AHA-Taiwan/2020_Taitung_Chulu-Between-Mountain-Clouds/002. Handbook/Constr-Process Handbook (pdf+ppt)/CBMC_Handbook.pdf

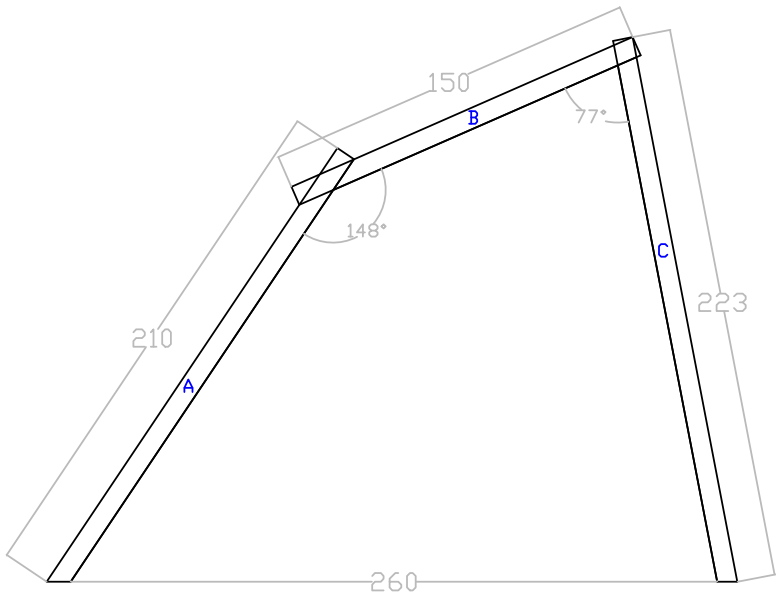
[picture p60: figure]
