AHA-Taiwan/2020_Taitung_Chulu-Between-Mountain-Clouds/002. Handbook/Constr-Process Handbook (pdf+ppt)/CBMC_Handbook.pdf

2020

# 初鹿義築．工作手冊

目錄

一．活動簡述．．．．．．．．．．．．１

二．自備物品與重要叮嚀．．．．．．．２

三．每日作息與行事曆．．．．．．．．４

四．交通與地圖．．．．．．．．．．．６

五．附件．．．．．．．．．．．．．．７

值日生班表

各組分工負責人

通訊錄

生活裝置設計圖面

木材尺寸

## 一．活動簡述

時間：2020年8月19日 —2020年8月28日

地點：台東縣卑南鄉初鹿國中（台東縣卑南鄉明峰村忠孝路2號） 住宿：初鹿國中圖書室

夏天是明亮的，太陽是辣的，
青春的心是熱血的。
離開了繁華，重返樸實；
捨棄了依賴，回歸自立。
參與團體 | 外界交流

俐場域建築設計

納樊司工作室

公東高工

家具木工科／室內設計科／建築科
義築工具圖書館

老麥農場露營區

台東縣政府文化處

社團法人台東縣巴蘭文化發展協會

社團法人台灣義築協會

聯新文教基金會

台東初鹿教會

行政院農委會林務局

正昌製材（台灣杉）

東皇昌五金行

材料贊助

１

## 二．自備物品與重要叮嚀

換洗衣物 | 輕便工作服／衣架／曬衣夾／塑膠袋／洗衣用具／肥皂
盥洗用品 | 潔牙用品／毛巾／沐浴用品／吹風機
個人衛生品 | 衛生紙／濕紙巾／生理用品
個人藥物 | 健保卡／防蚊液／防曬乳／藥膏／個人用藥
必備物品 | 手電筒／睡袋／麥克筆／抹布
餐具 | 環保餐具／水壺
其他 | 帽子／外套／雨具／筆記／糧食／相機／袖套 足夠的零用金＆快樂心
1. 校園蛇類出沒，夜間活動務必攜帶手電筒，並尊重當地生態環境 。
2. 為避免影響施工進度，請按作息表活動，請勿飲酒 。
3. 避免使用香味濃郁的盥洗用品，易引來蚊蟲 。
4. 請留意貴重物品 。
5. 請注意當地禁忌，活動請結伴同行 。
6. 當地提款與融資服務不便，請攜帶足夠的現金 。
7. 施工區域內請勿穿脫鞋或涼鞋，並時時補充水分。
8. 由於浴室數量有限，洗澡時間限制十分鐘。

重要叮嚀

２

施工注意事項

最重要的三件事！！

1. 晚間收工前30分鐘，清點材料、工具
2. 收工前15分鐘，整理工作環境
3. 工地危險，務必攜帶安全帽，勿著涼拖鞋

-工具配件務必妥善放回它的位置，切勿亂放

-建材勿隨意放置，會影響材料品質與建築壽命

-廢料勿扔棄，做好資源管理，這是對建築過程的尊重

-離隊務必告知組員、組長，個人行為將影響全體

-注意言行、態度，對自己負責，也尊重合作夥伴

-我們是一個大團體，務必保持與其他單位的良好互動

-我們是一個共同體，請關心身邊的伙伴，發揮自己的價值

做一個謙卑的實踐者，感恩這份學習的機會

３

## 三．每日作息與行事曆

時間 | 活動 | 備註
0600 | Good Morning | 宿舍長叫醒大家
0600–0630 | 盥洗準備
0630–0700 | 活力早餐 | 生活組提前準備
0700–1130 | 木構GO GO！ | 施工組開工
1130–1300 | 午餐充電 | 生活組準備
1300–1700 | 木構GO GO GO！ | 施工組開工
1700–1800 | 洗澎澎 | 超時斷水電！
1800–1930 | 晚餐時光 | 生活組準備
1930–2100 | 工作會議 | 進度／工地狀況檢討
2100–2200 | 小組／個人時間 | 工作日誌／影音整理
2200 | 睡飽睡好

生活值日生工作

1. 工作環境整理
2. 餐後、廚餘整理
3. 清洗、收拾餐具
4. 搬運、發放食物

住宿值日生工作

1. 寢室環境清潔
2. 廁所清潔及垃圾清理
3. 浴廁清潔

４

（時間可能依每日天候狀況有所調整）

08/19 （三）

08/20 （四）

08/21 （五）

08/22 （六）

行事曆

５

認識大家／基礎前置加工

08/23 （日）

08/24 （一）

08/26 （三）

08/25 （二）

08/28 （五）

08/27 （四）

基礎前置加工／放樣／灌漿

木料分類標號／尺寸標記

木構單元與基礎固定

木料加工：斬斷／引孔／導角

木構系統單元化組裝

木構系統單元化組裝

木料加工：斬斷／引孔／導角

表面處理／護木漆／環境清潔

表面處理／護木漆／環境清潔／撤收

## 四．交通與地圖

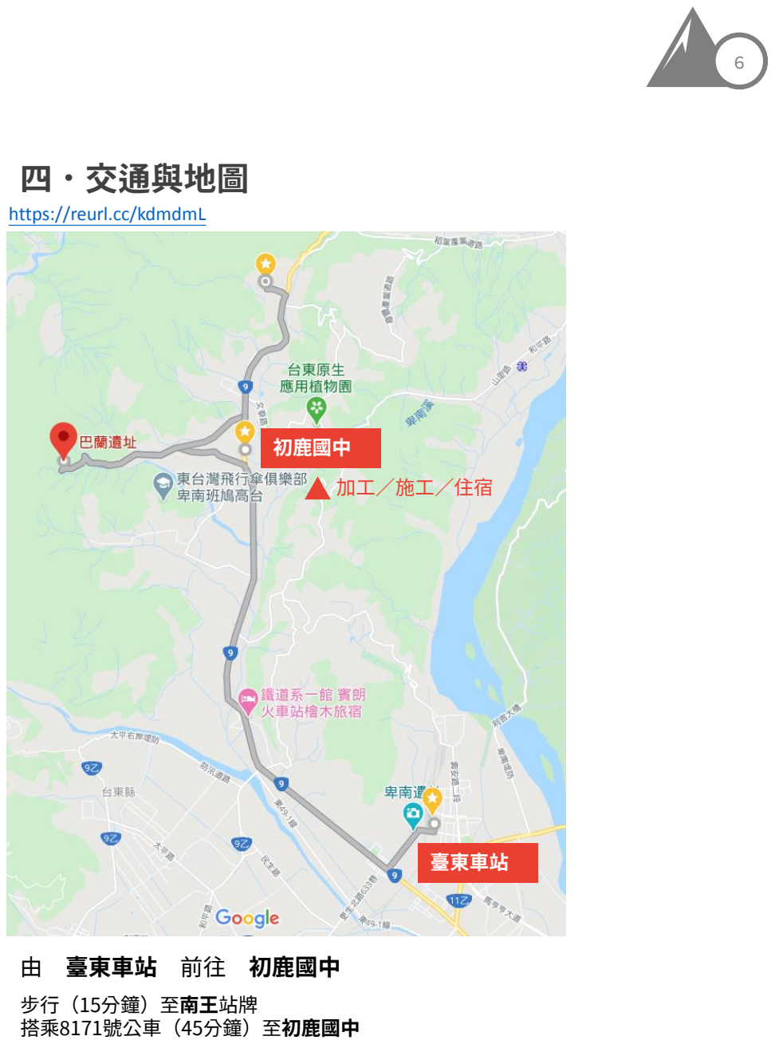
[picture p39: page 8]

由 臺東車站 前往 初鹿國中

初鹿國中

臺東車站

加工／施工／住宿

步行（15分鐘）至南王站牌
搭乘8171號公車（45分鐘）至初鹿國中

６

https://reurl.cc/kdmdmL

日期 | 生活值日生 | 住宿值日生
8/19 | 瑋聖 仁楷 | 正威 昊翰
8/20 | 偵慧 文慧 | 玥綾 柏翔
8/21 | 仁楷 正威 | 昊翰 震洋
8/22 | 文慧 玥綾 | 柏翔 甫亘
8/23 | 正威 昊翰 | 震洋 瑋聖
8/24 | 玥綾 柏翔 | 甫亘 偵慧
8/25 | 昊翰 震洋 | 瑋聖 仁楷
8/26 | 柏翔 甫亘 | 偵慧 文慧
8/27 | 震洋 瑋聖 | 仁楷 正威
8/28 | 甫亘 偵慧 | 文慧 玥綾

值日生班表

８

N1 | N2

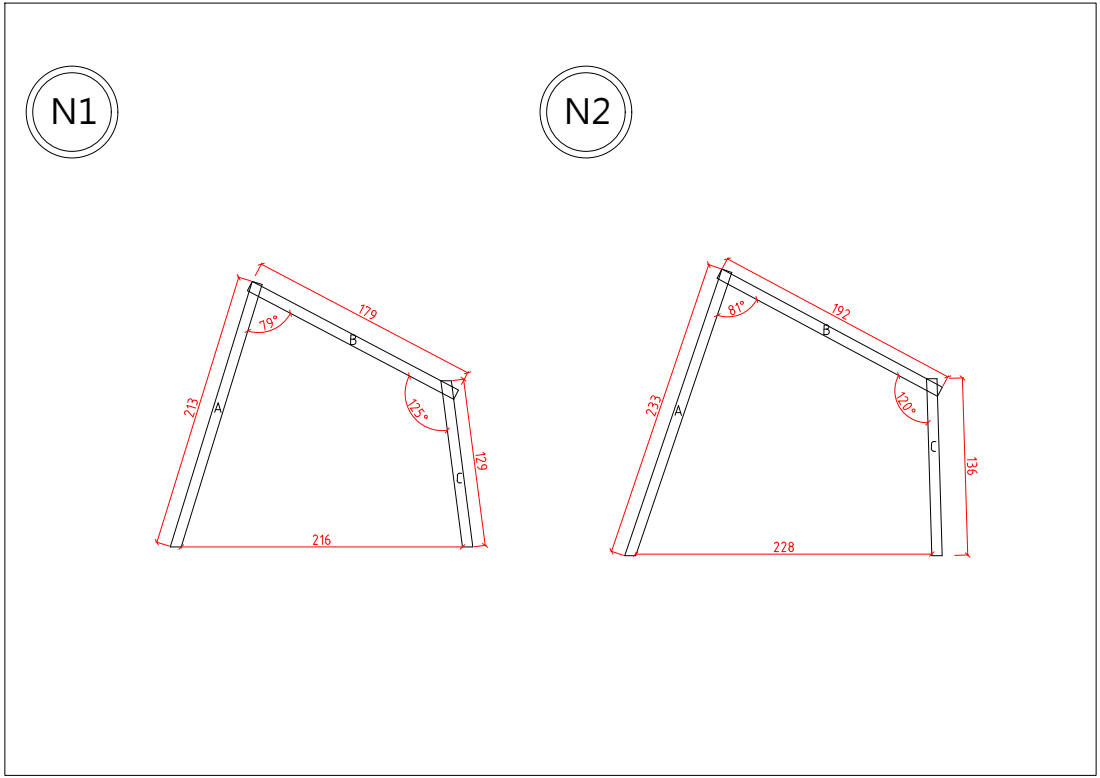
[picture p40: page 10]

N3 | N4

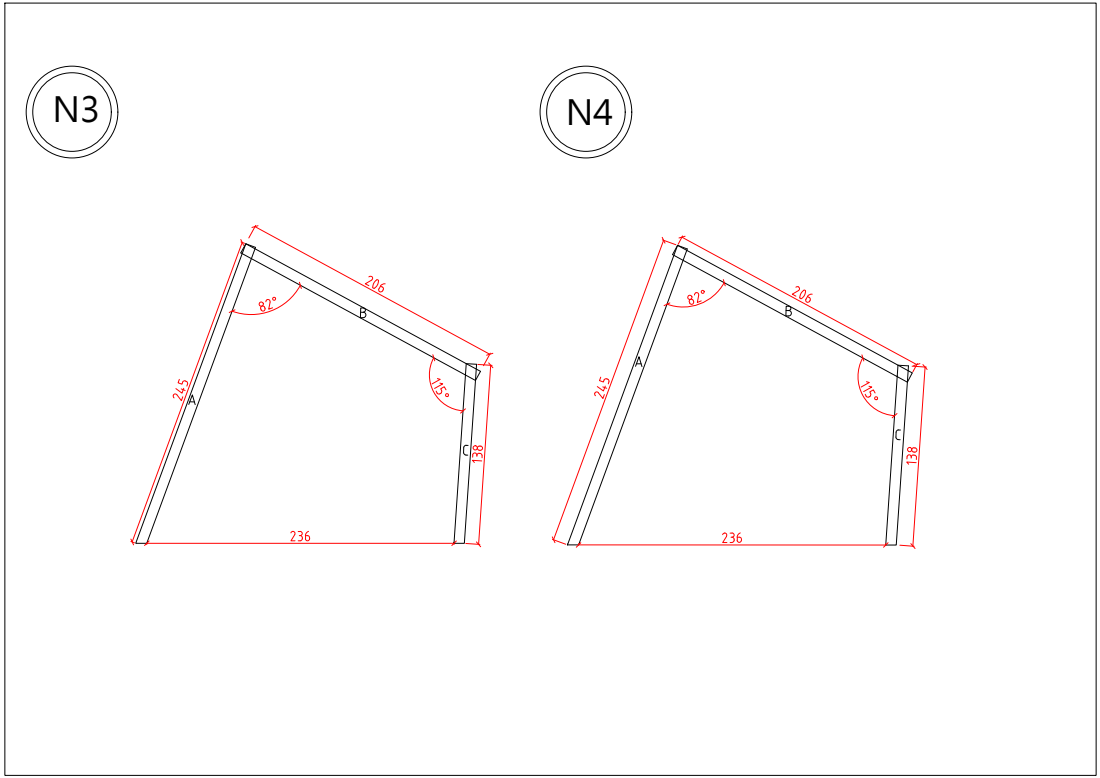
[picture p41: page 11]

N5 | N6

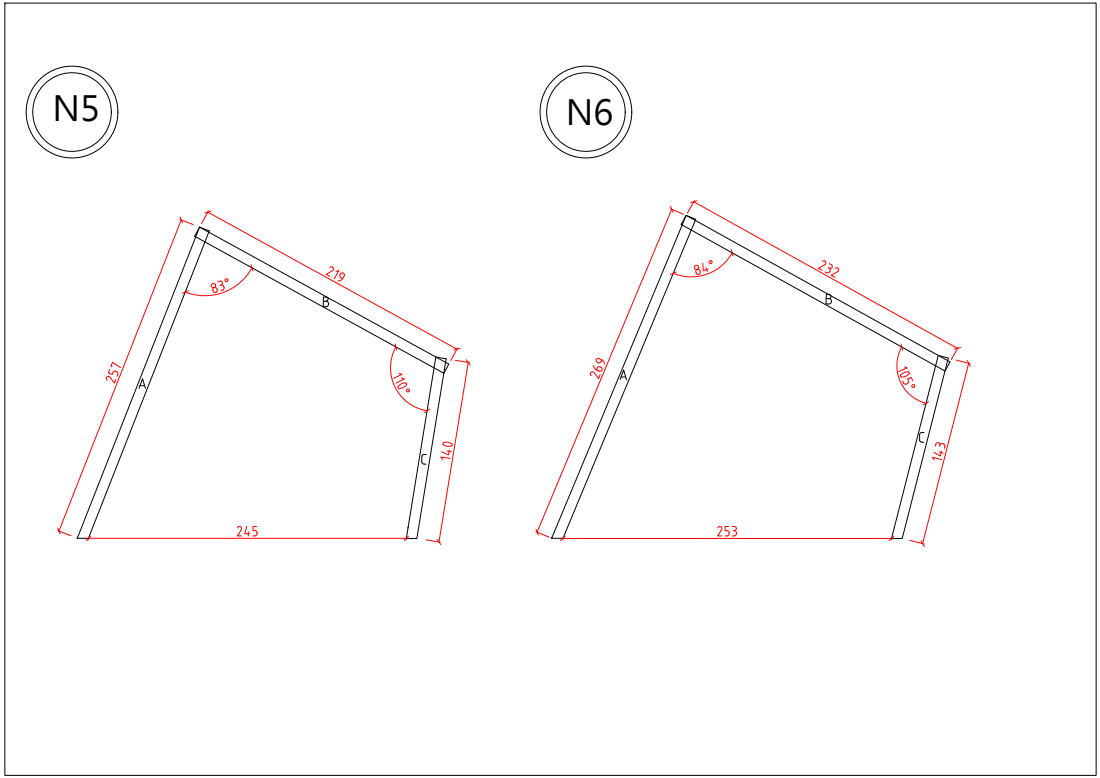
[picture p42: page 12]

N7 | N8

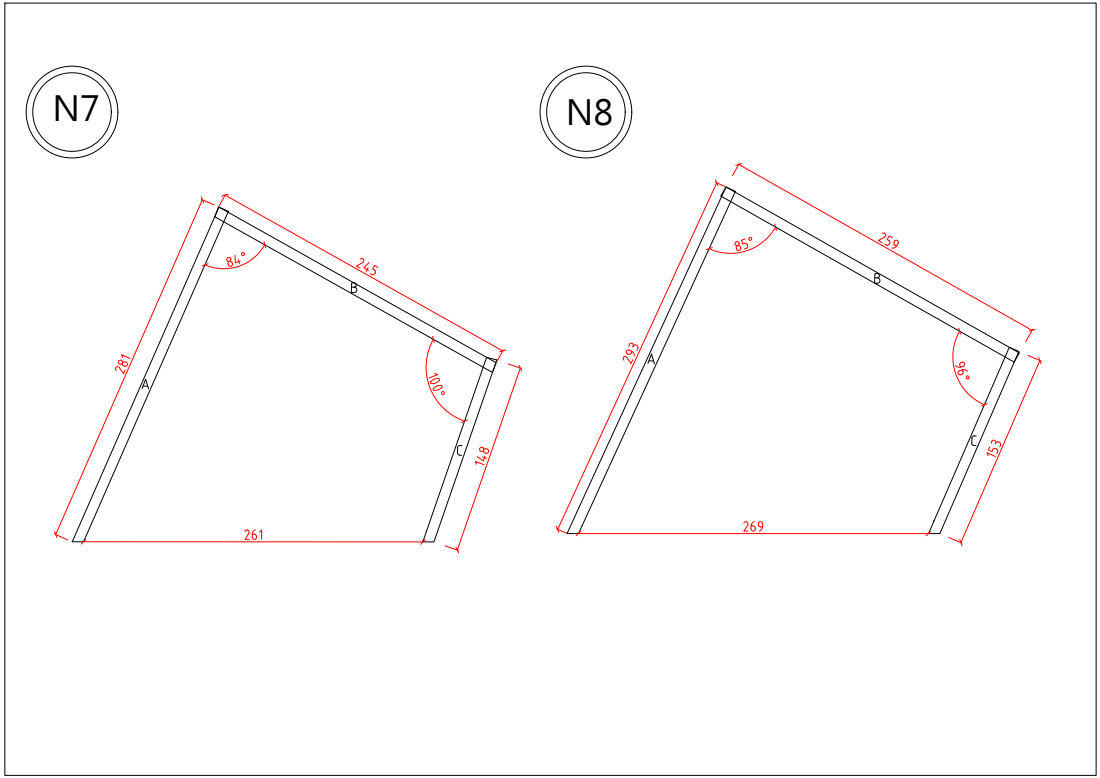
[picture p43: page 13]

N9 | N10

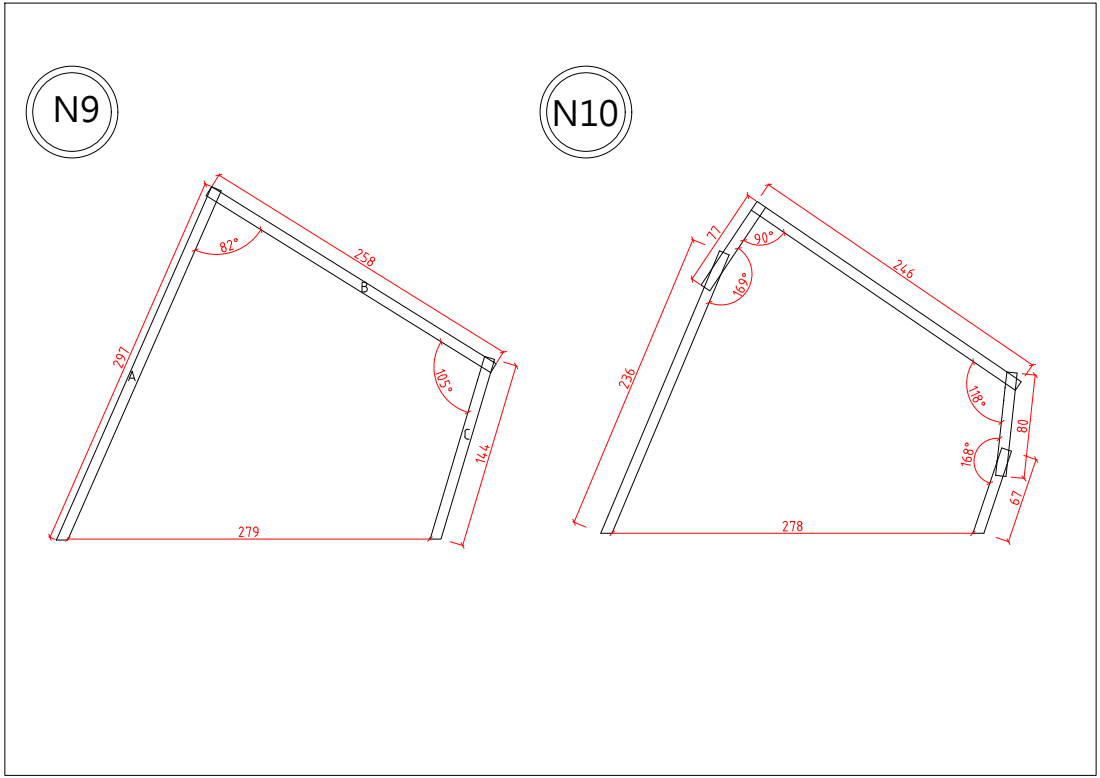
[picture p44: page 14]

N11 | N12

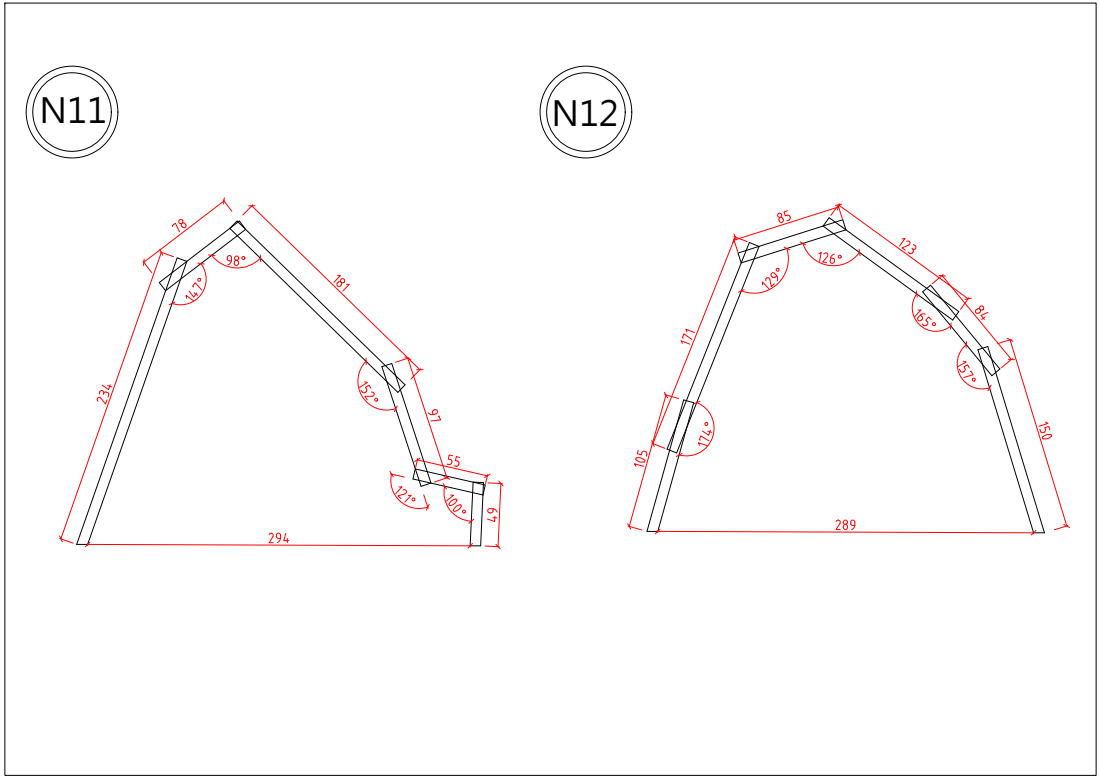
[picture p45: page 15]

N13

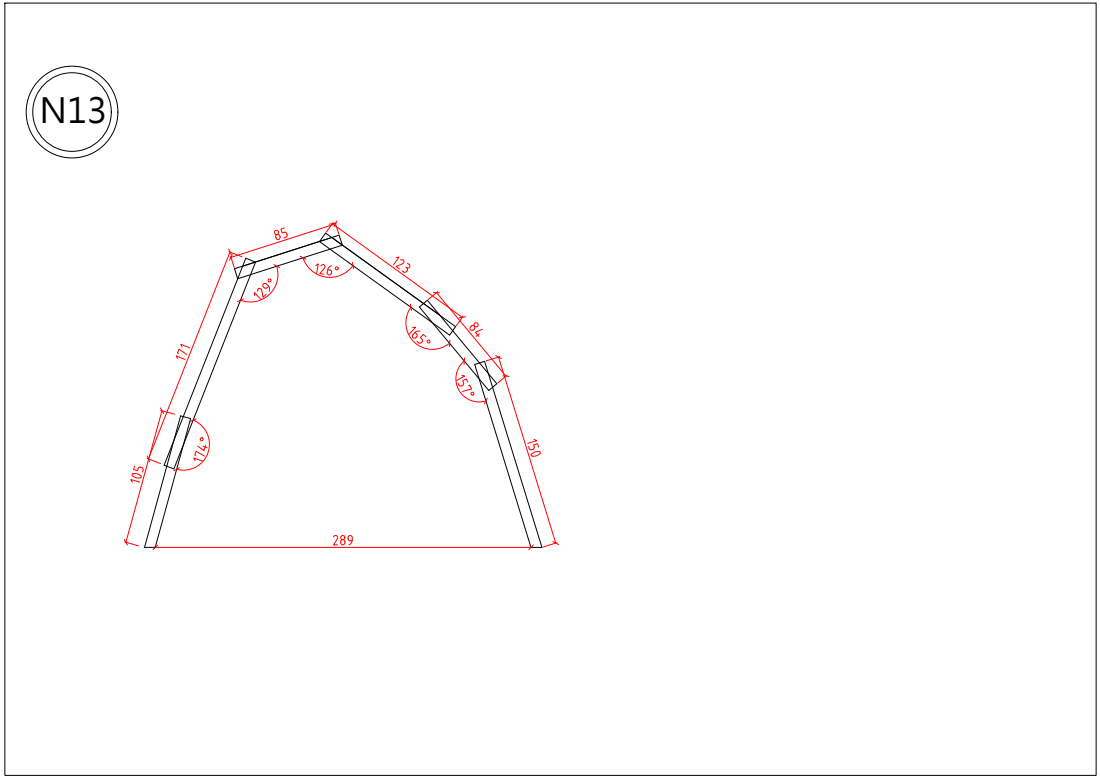
[picture p46: page 16]

N14 | N15

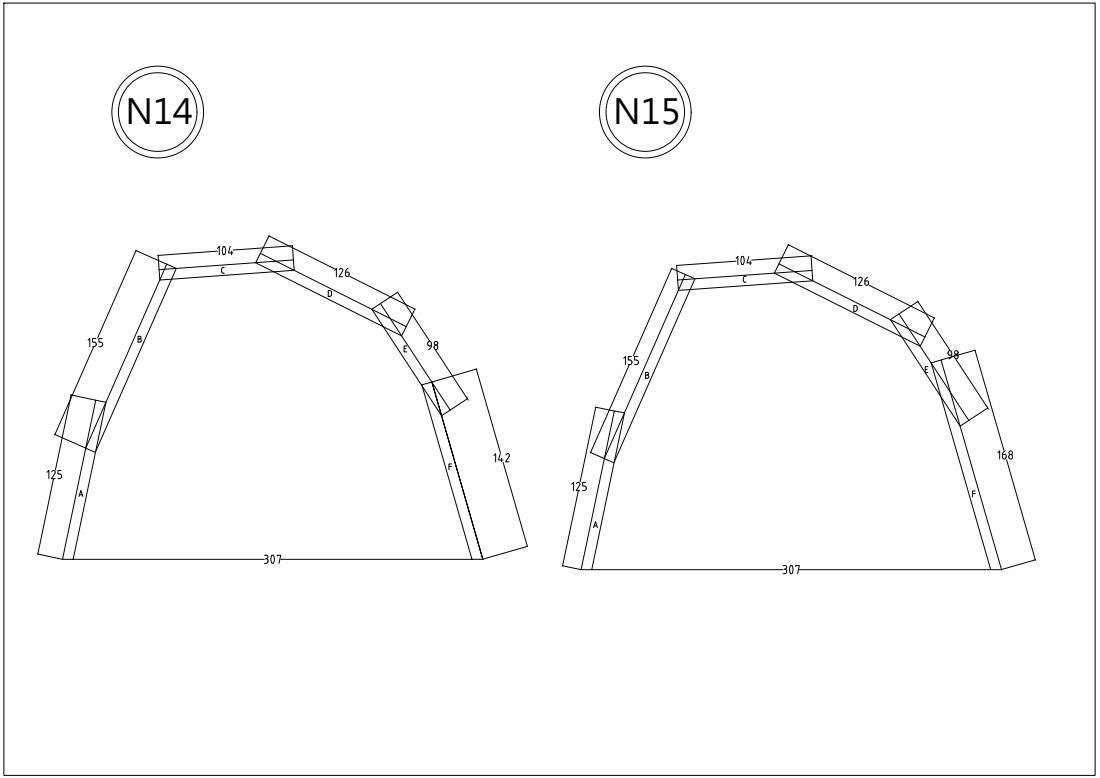
[picture p47: page 17]

N16 | N17 | N18 | N19

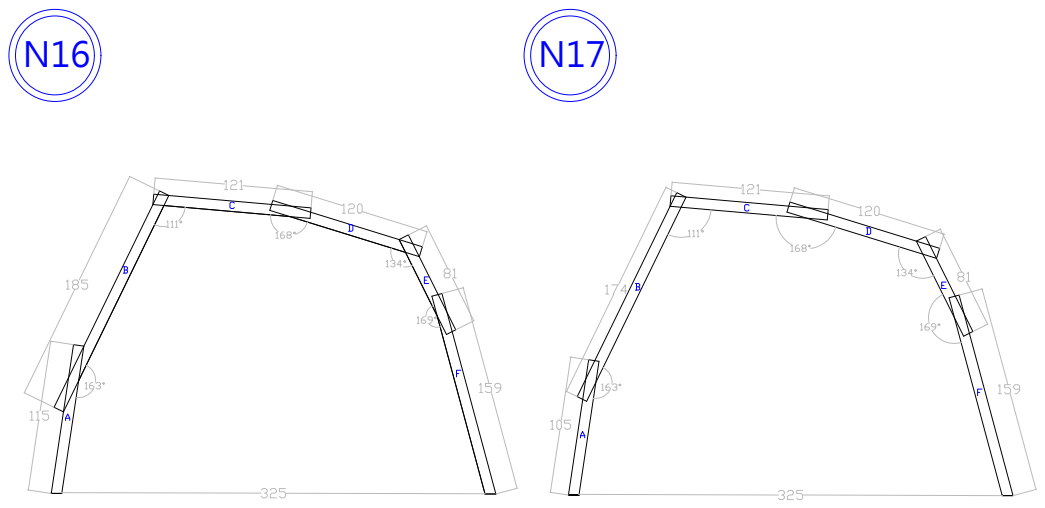
[picture p48: page 18]

N18 | N19

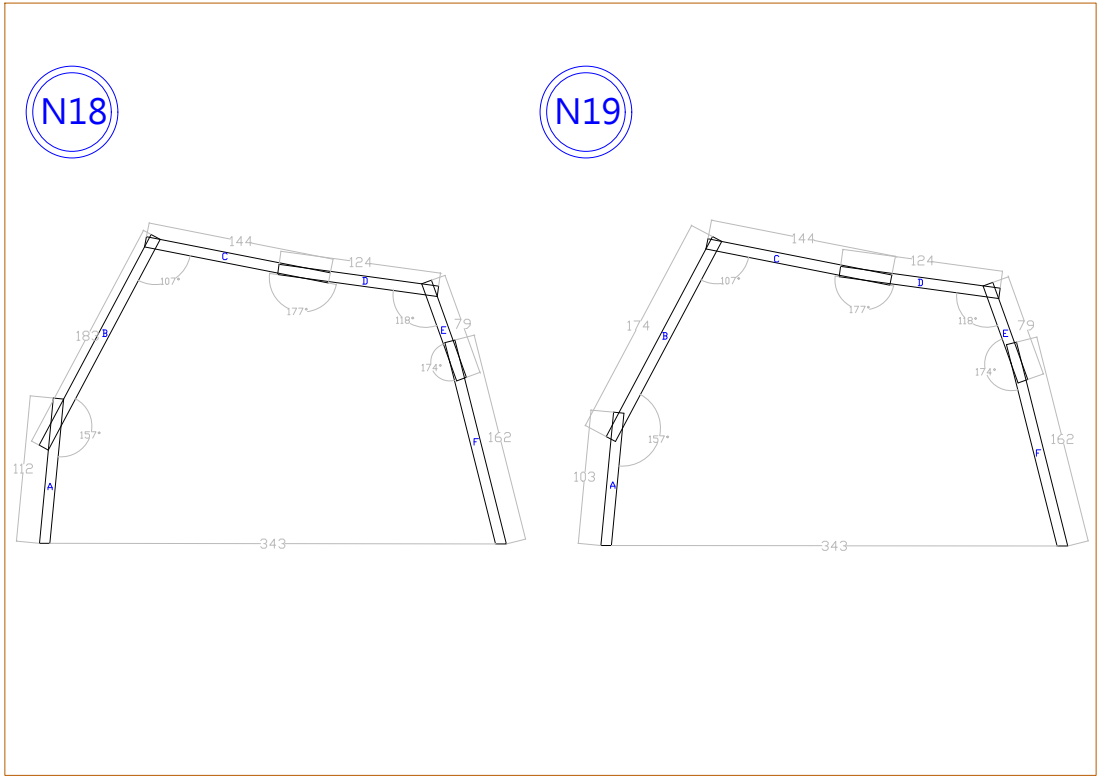
[picture p49: page 19]

N20

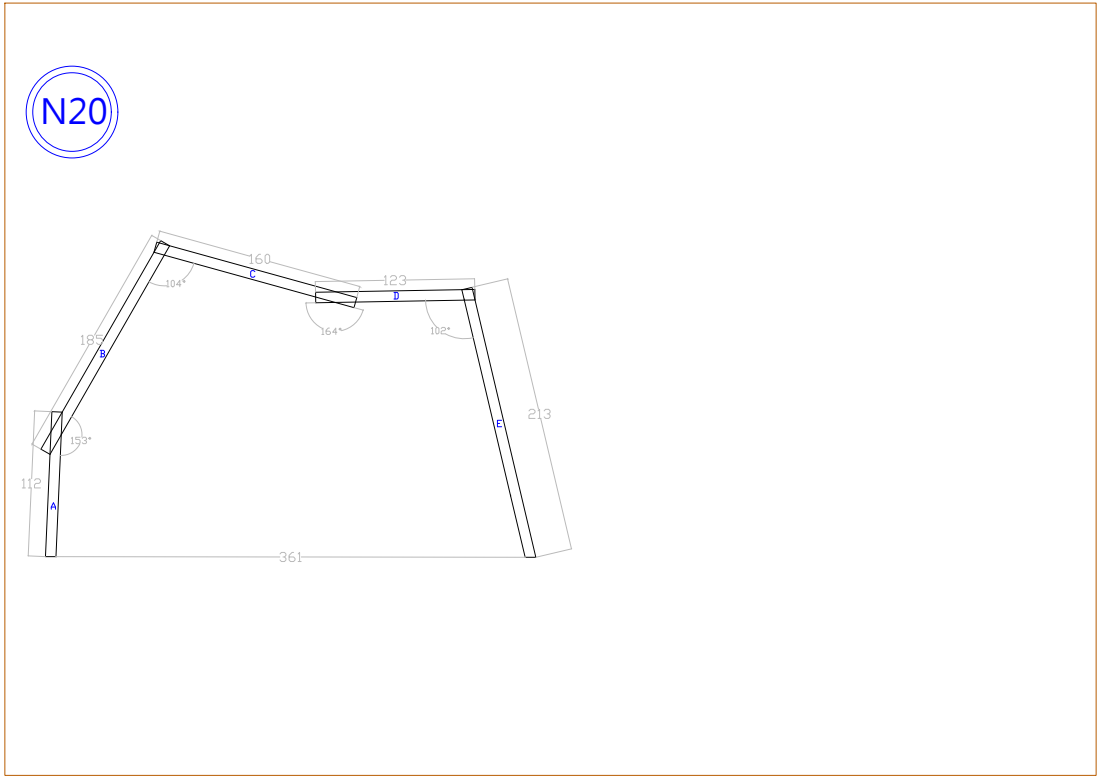
[picture p50: page 20]

N21 | N22

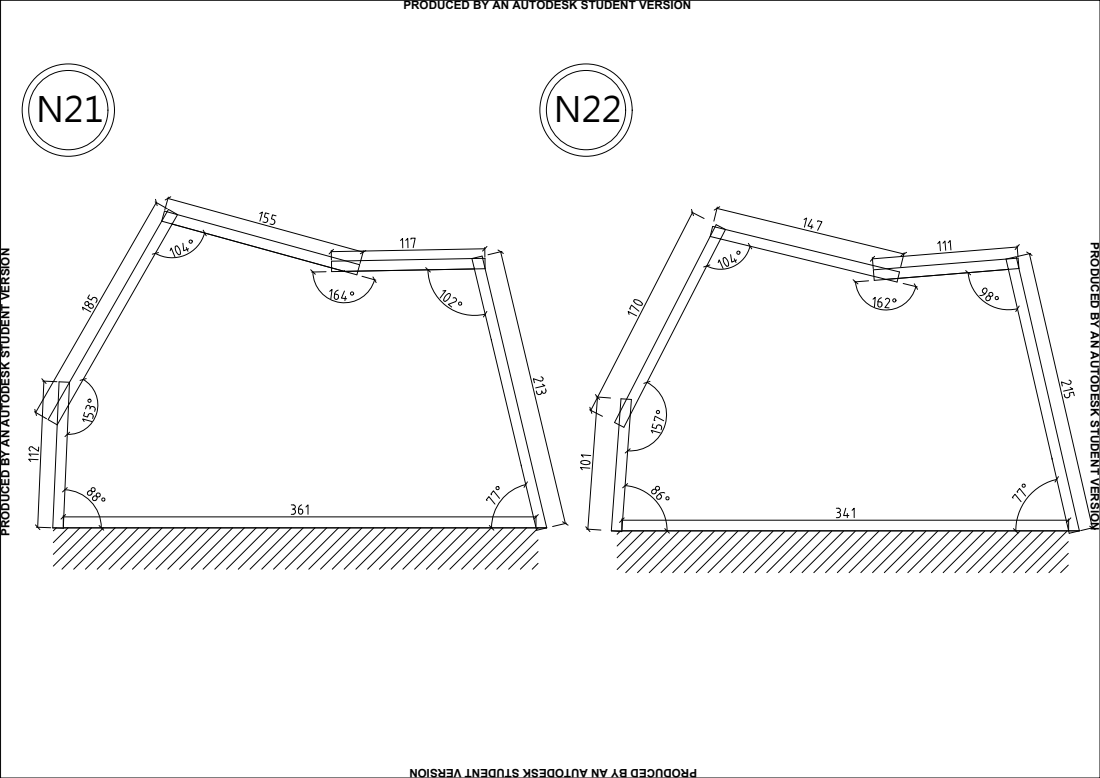
[picture p51: page 21]

PRODUCED BY AN AUTODESK STUDENT VERSION

N23 | N24

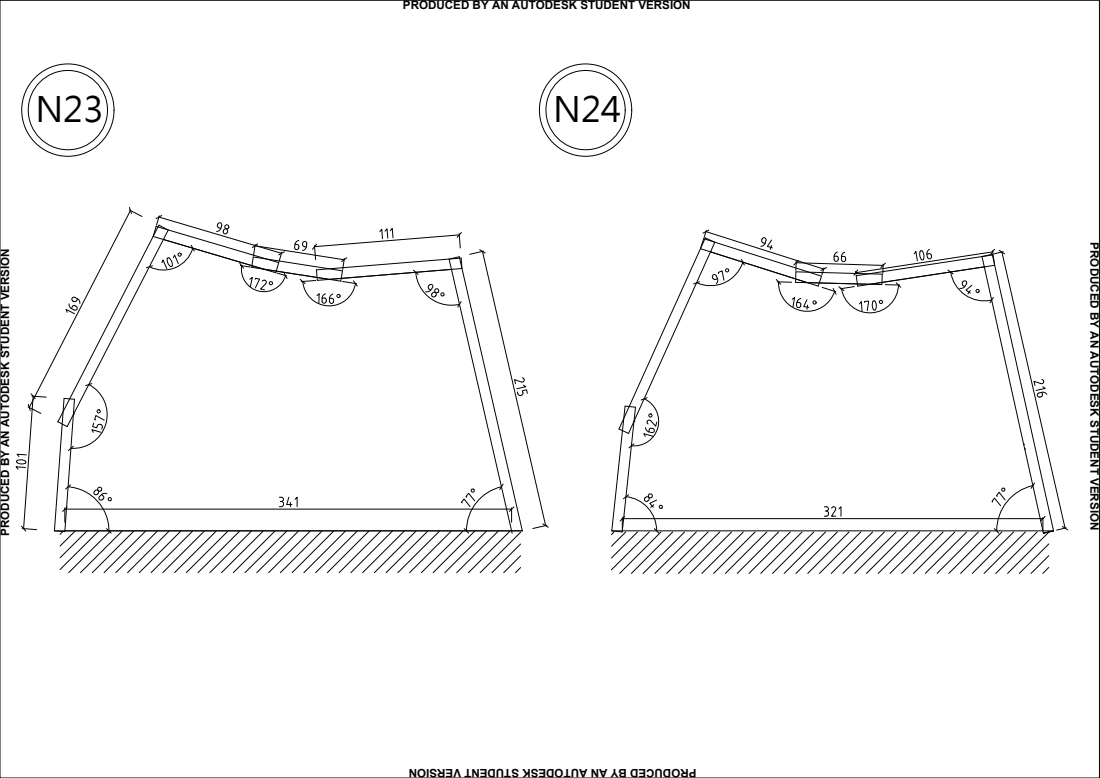
[picture p52: page 22]

PRODUCED BY AN AUTODESK STUDENT VERSION

N25 | N26

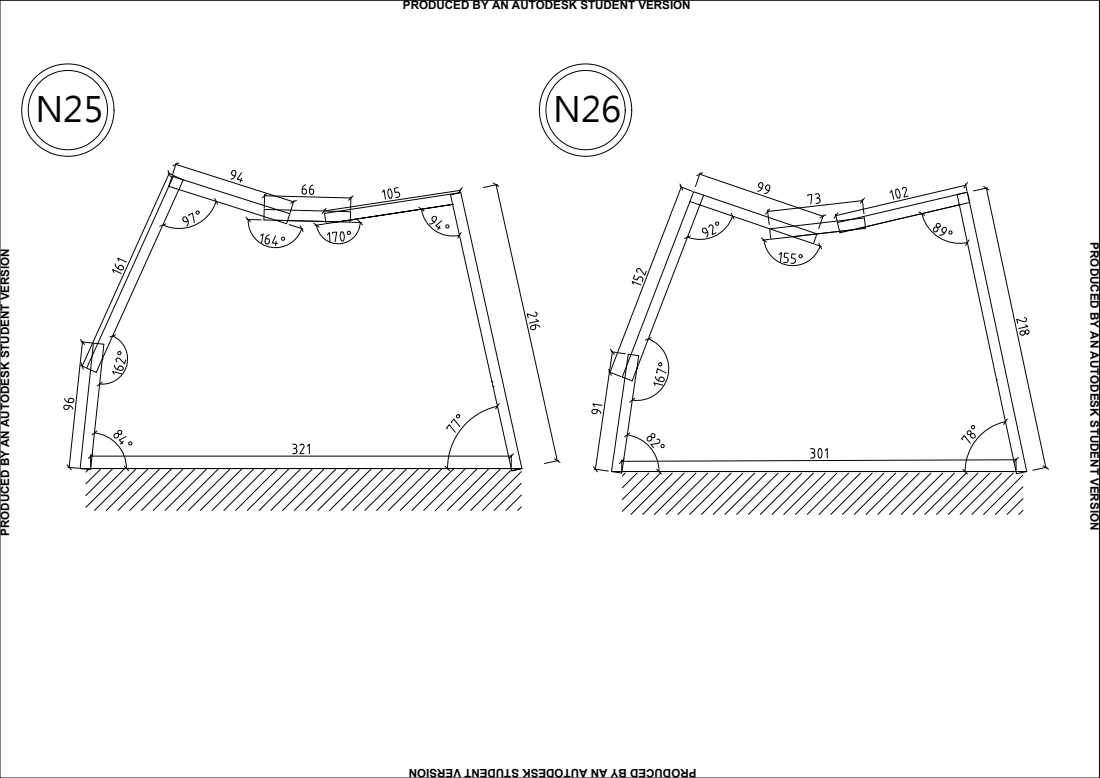
[picture p53: page 23]

PRODUCED BY AN AUTODESK STUDENT VERSION

N27 | N28

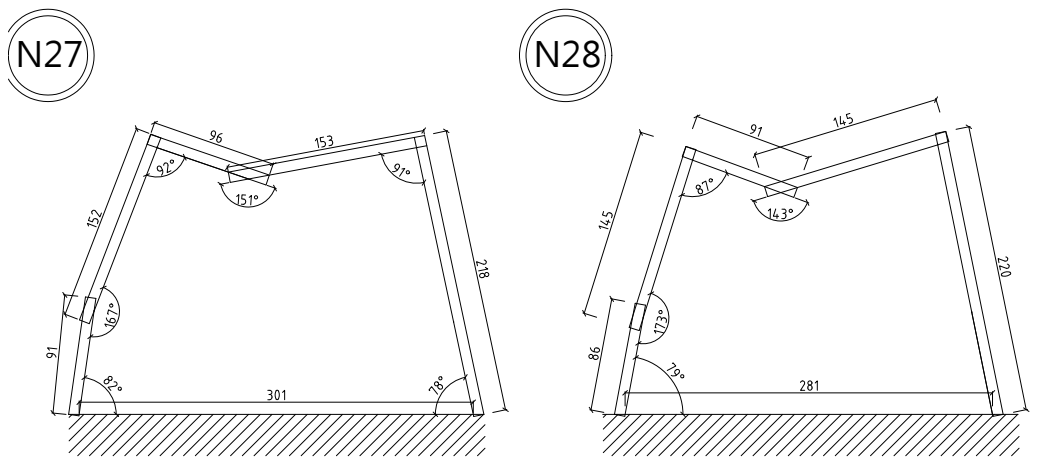
[picture p54: page 24]

N29 | N30

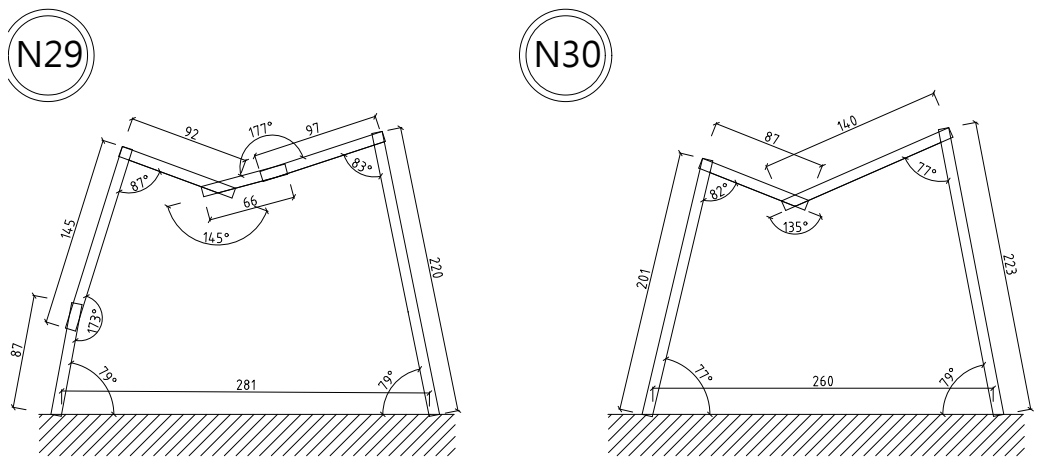
[picture p55: page 25]

N31 | N32

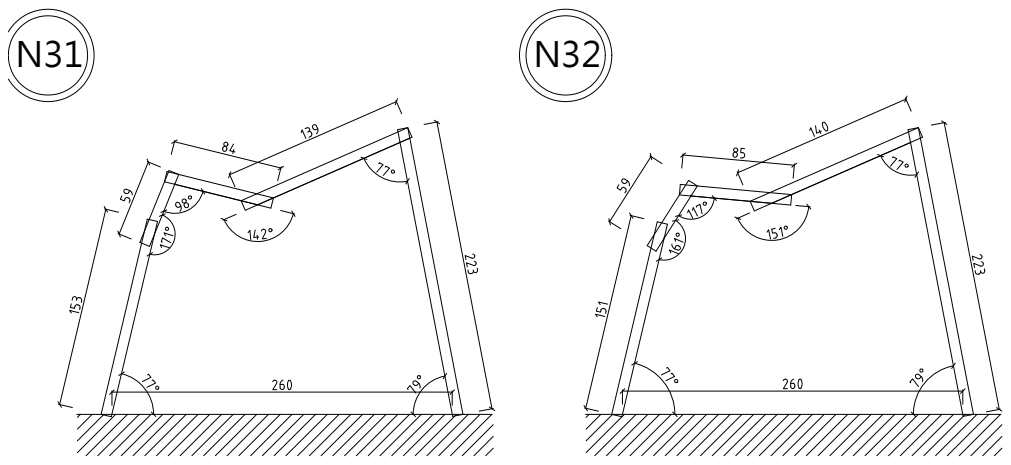
[picture p56: page 26]

N33 | N34

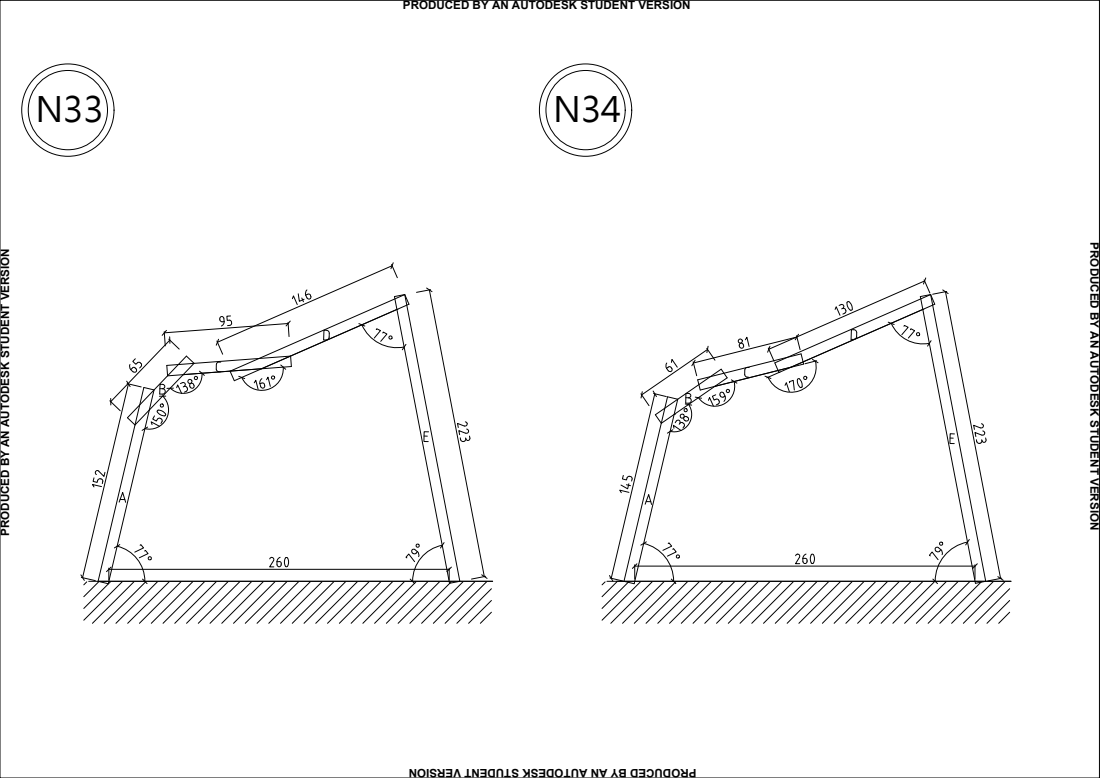
[picture p57: page 27]

PRODUCED BY AN AUTODESK STUDENT VERSION

N35 | N36

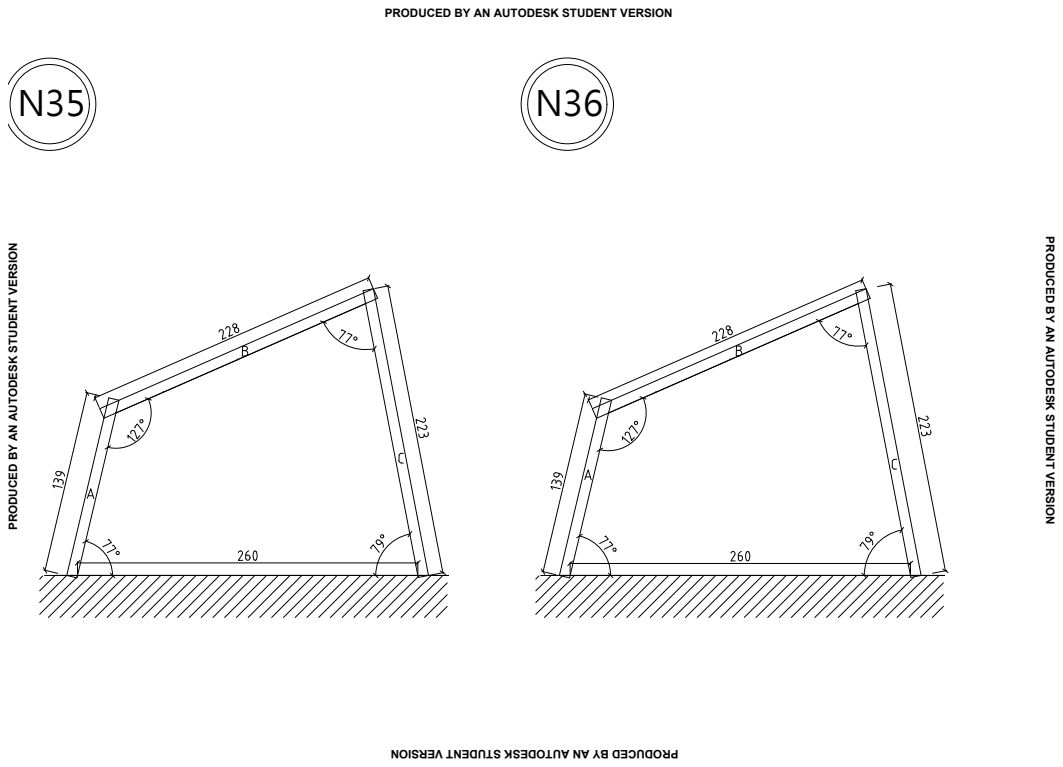
[picture p58: page 28]

PRODUCED BY AN AUTODESK STUDENT VERSION

N37 | N38


N40 | N41

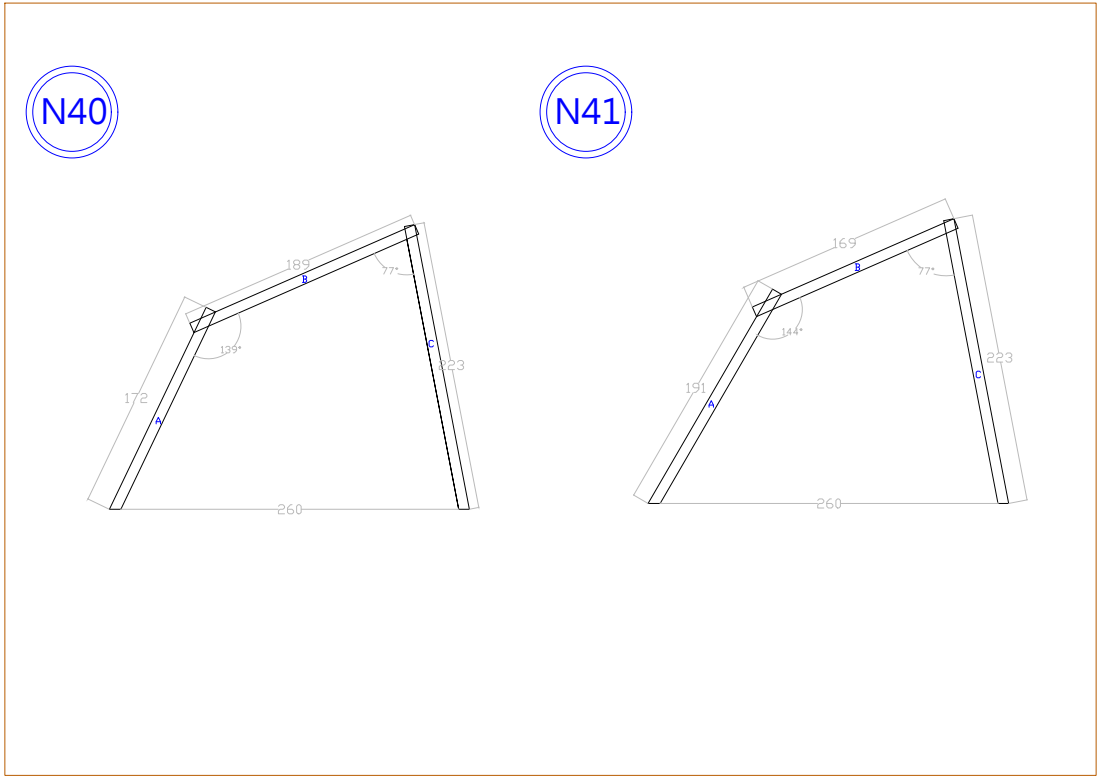
[picture p59: page 30]

N42
